rowyfol/eleckI_uni/KiCad/elec101.kicad_sch

## KiCad design KiCad/elec101.kicad_sch (2026-06-19)

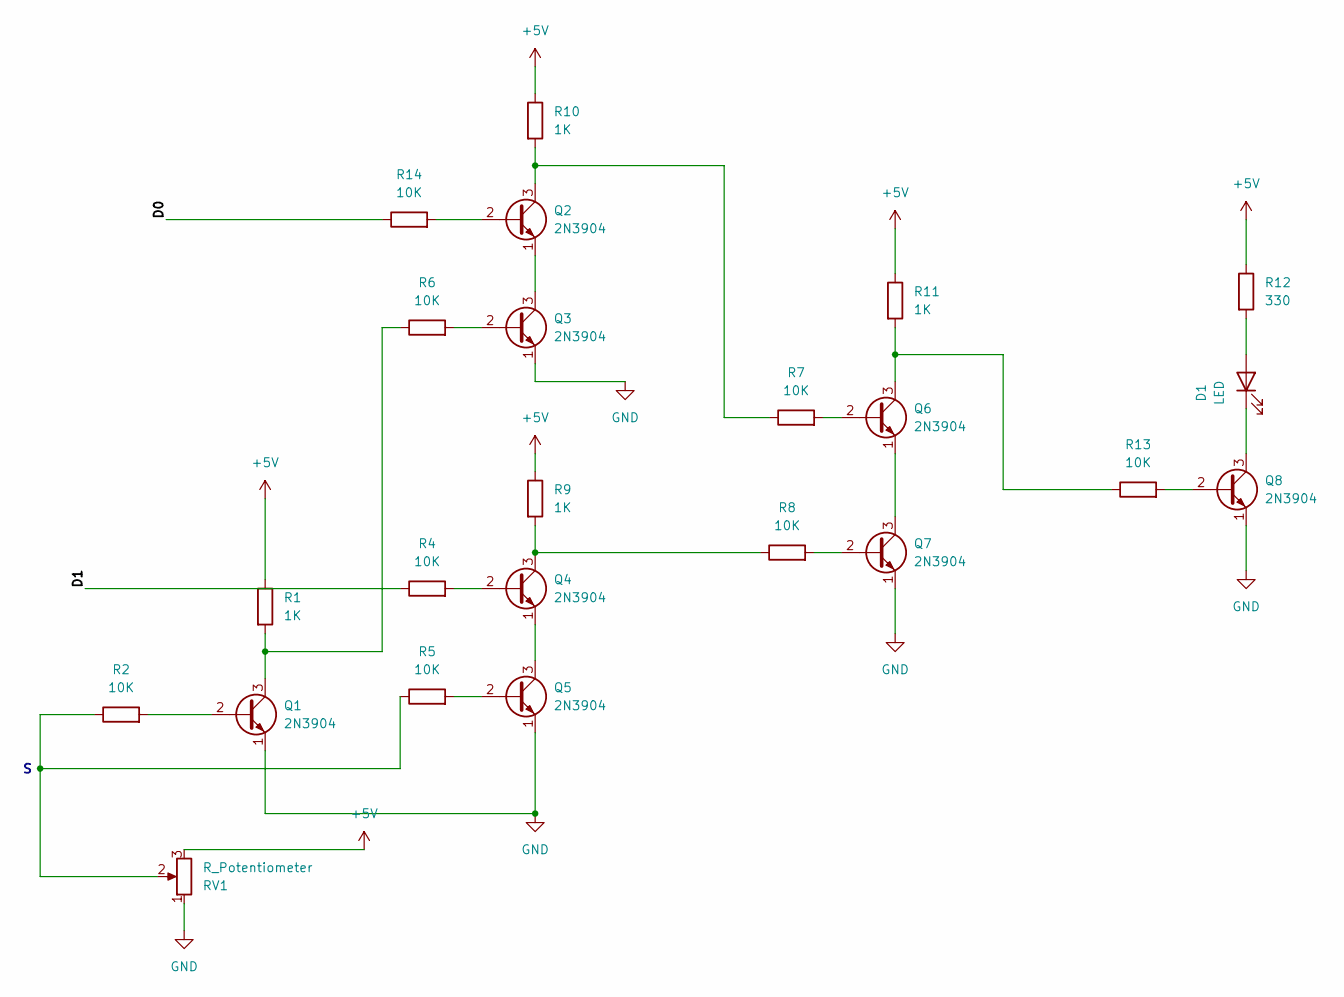
[picture p6: schematic elec101.kicad_sch]

Parts:
D1: LED
Q1, Q2, Q3, Q4, Q5, Q6, Q7, Q8: 2N3904; TO-92_Inline
R1, R9, R10, R11: 1K
R2, R4, R5, R6, R7, R8, R13, R14: 10K
R12: 330
RV1: R_Potentiometer

Connections:
+5V: R1.1, R9.1, R10.1, R11.1, R12.1, RV1.3
D0: R14.1
D1: R4.1
GND: Q1.1 (E), Q3.1 (E), Q5.1 (E), Q7.1 (E), Q8.1 (E), RV1.1
unnamed: D1.1 (K), Q8.3 (C)
unnamed: D1.2 (A), R12.2
unnamed: Q1.2 (B), R2.2
unnamed: Q1.3 (C), R1.2, R6.1
unnamed: Q2.1 (E), Q3.3 (C)
unnamed: Q2.2 (B), R14.2
unnamed: Q2.3 (C), R7.1, R10.2
unnamed: Q3.2 (B), R6.2
unnamed: Q4.1 (E), Q5.3 (C)
unnamed: Q4.2 (B), R4.2
unnamed: Q4.3 (C), R8.1, R9.2
unnamed: Q5.2 (B), R5.2
unnamed: Q6.1 (E), Q7.3 (C)
unnamed: Q6.2 (B), R7.2
unnamed: Q6.3 (C), R11.2, R13.1
unnamed: Q7.2 (B), R8.2
unnamed: Q8.2 (B), R13.2
unnamed: R2.1, R5.1, RV1.2
